vives-project-xp/HandheldRetropie/Circuits_Diagrams/architectureDocument/architecture_update3.png

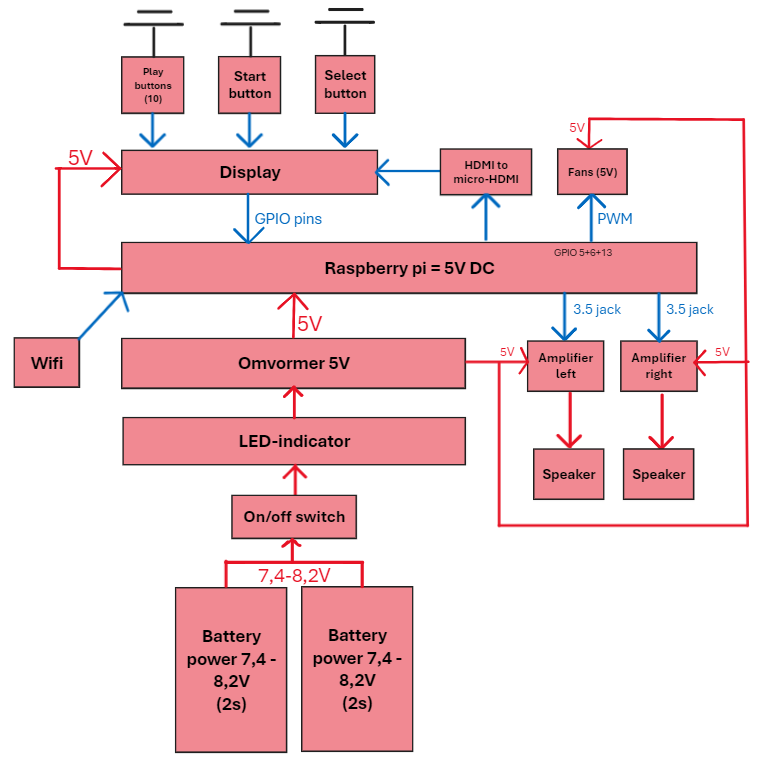
Circuits_Diagrams/architectureDocument/architecture_update3.png
