vives-project-xp/HandheldRetropie/Circuits_Diagrams/electrical_circuit/simple_electrical.png

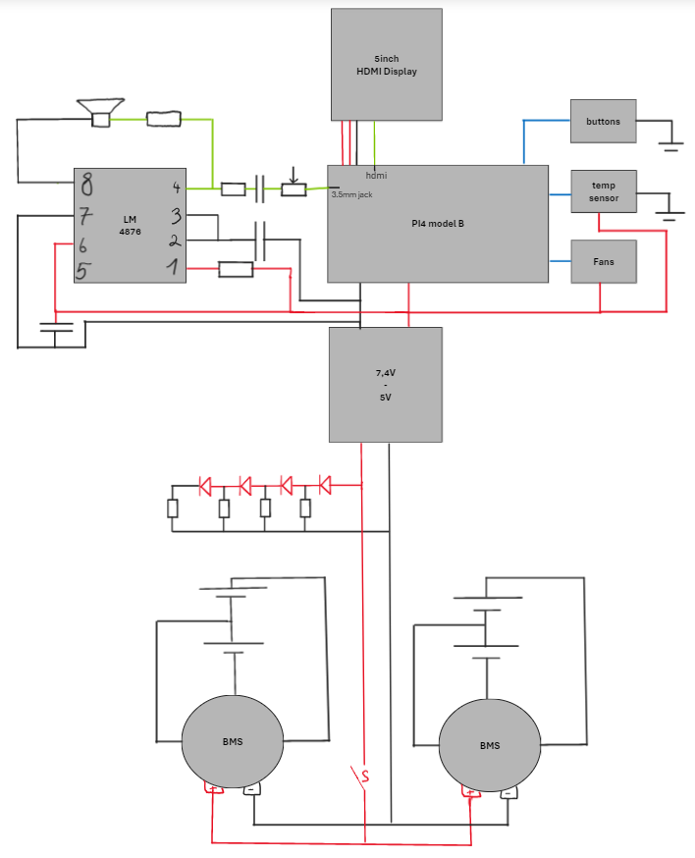
Circuits_Diagrams/electrical_circuit/simple_electrical.png
