vives-project-xp/HandheldRetropie/Circuits_Diagrams/PCB_Schema/Schermafbeelding 2024-05-21 214417.png

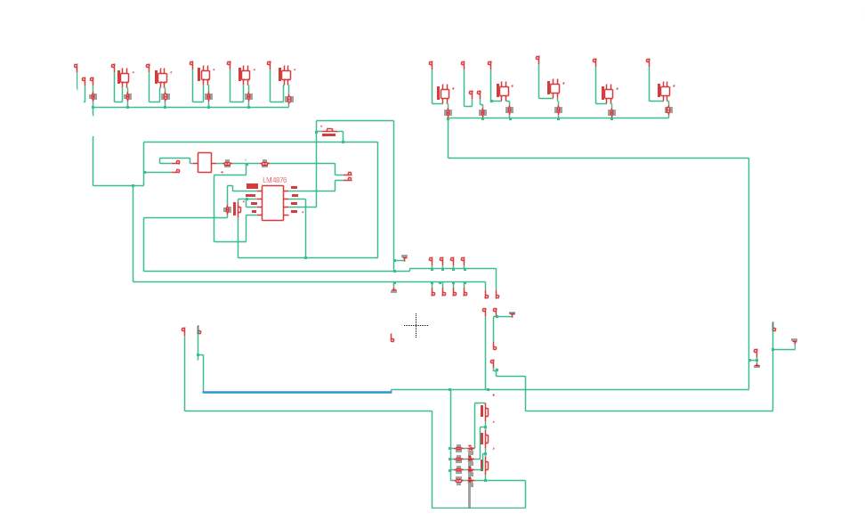
Circuits_Diagrams/PCB_Schema/Schermafbeelding 2024-05-21 214417.png
