vives-project-xp/HandheldRetropie/Components_choises/pictures/amp_cond_1.png

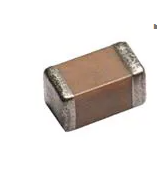
Components_choises/pictures/amp_cond_1.png
